intoxication/WirelessRelay/Firmware/config.h

#ifndef _CONFIG_H_
#define _CONFIG_H_

#define SSID "wifi-SSID"
#define PASSWORD "password"
#define HOST "192.168.1.255"
#define PORT 15000

//#define PIN_OFFSET 0
#define PIN_OFFSET 17

//const char DEVICE_ID[] PROGMEM  =  "70D9A386-9D32-46A6-910D-E029EF3B0E9E";
const char DEVICE_ID[] PROGMEM  =  "217BBD37-E4BF-4D8A-A43B-3887F68350EA";

#endif //_CONFIG_H_
